cycfi/xr/XR_Controls/Blend_Control/Blend_Control_BOM.pdf

BLEND CONTROL
Item | Description | Part Number | Packaging | Manufacturer | Location | Qty.
1 | 25K Potentiometer | PDB181-GTR01-253A2 (http://www.mouser.ph/ProductDetail/Bourns/PDB181-GTR01-253A2/) | - | Bourns | POT1 | 1
2 | 1x3 SMD Male Header | M20-8900305 (http://www.mouser.ph/ProductDetail/Harwin/M20-8900305/) | 2.54mm | Harwin | H1 | 1
