cycfi/xr/XR_Controls/Volume_Control/Volume_Control_BOM.pdf

VOLUME CONTROL
Item | Description | Part Number | Packaging | Manufacturer | Location | Qty.
1 | 25K Potentiometer | PDB241-GTR01-253A2 (http://www.mouser.com/ProductDetail/Bourns/PDB241-GTR01-253A2/) | - | Bourns | POT1 | 1
2 | 1x5 SMD Male Header | M20-8900505 (http://www.mouser.com/ProductDetail/Harwin/M20-8900505/) | 2.54mm | Harwin | H1 | 1
