cycfi/xr/XR_Controls/Tone_Control/Tone_Control_BOM.pdf

TONE CONTROL
Item | Description | Part Number | Packaging | Manufacturer | Location | Qty.
1 | 25K Potentiometer | PDB181-GTR01-253A2 (http://www.mouser.ph/ProductDetail/Bourns/PDB181-GTR01-253A2/) | - | Bourns | POT1 | 1
2 | 1x2 Male Header RA | M20-9960245 (http://www.mouser.ph/ProductDetail/Harwin/M20-9960245/) | 2.54mm | Harwin | H1 | 1
3 | 0.1uF | VJ0603Y104JXJPW1BC (http://www.mouser.ph/ProductDetail/Vishay-Vitramon/VJ0603Y104JXJPW1BC/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) | SMD 0603 | Vishay | C1 | 1
