cycfi/xr/5_Way_Flex_Switch/Configuration_board/Configuration_board_A/Configuration_Board_A_Schematics.pdf

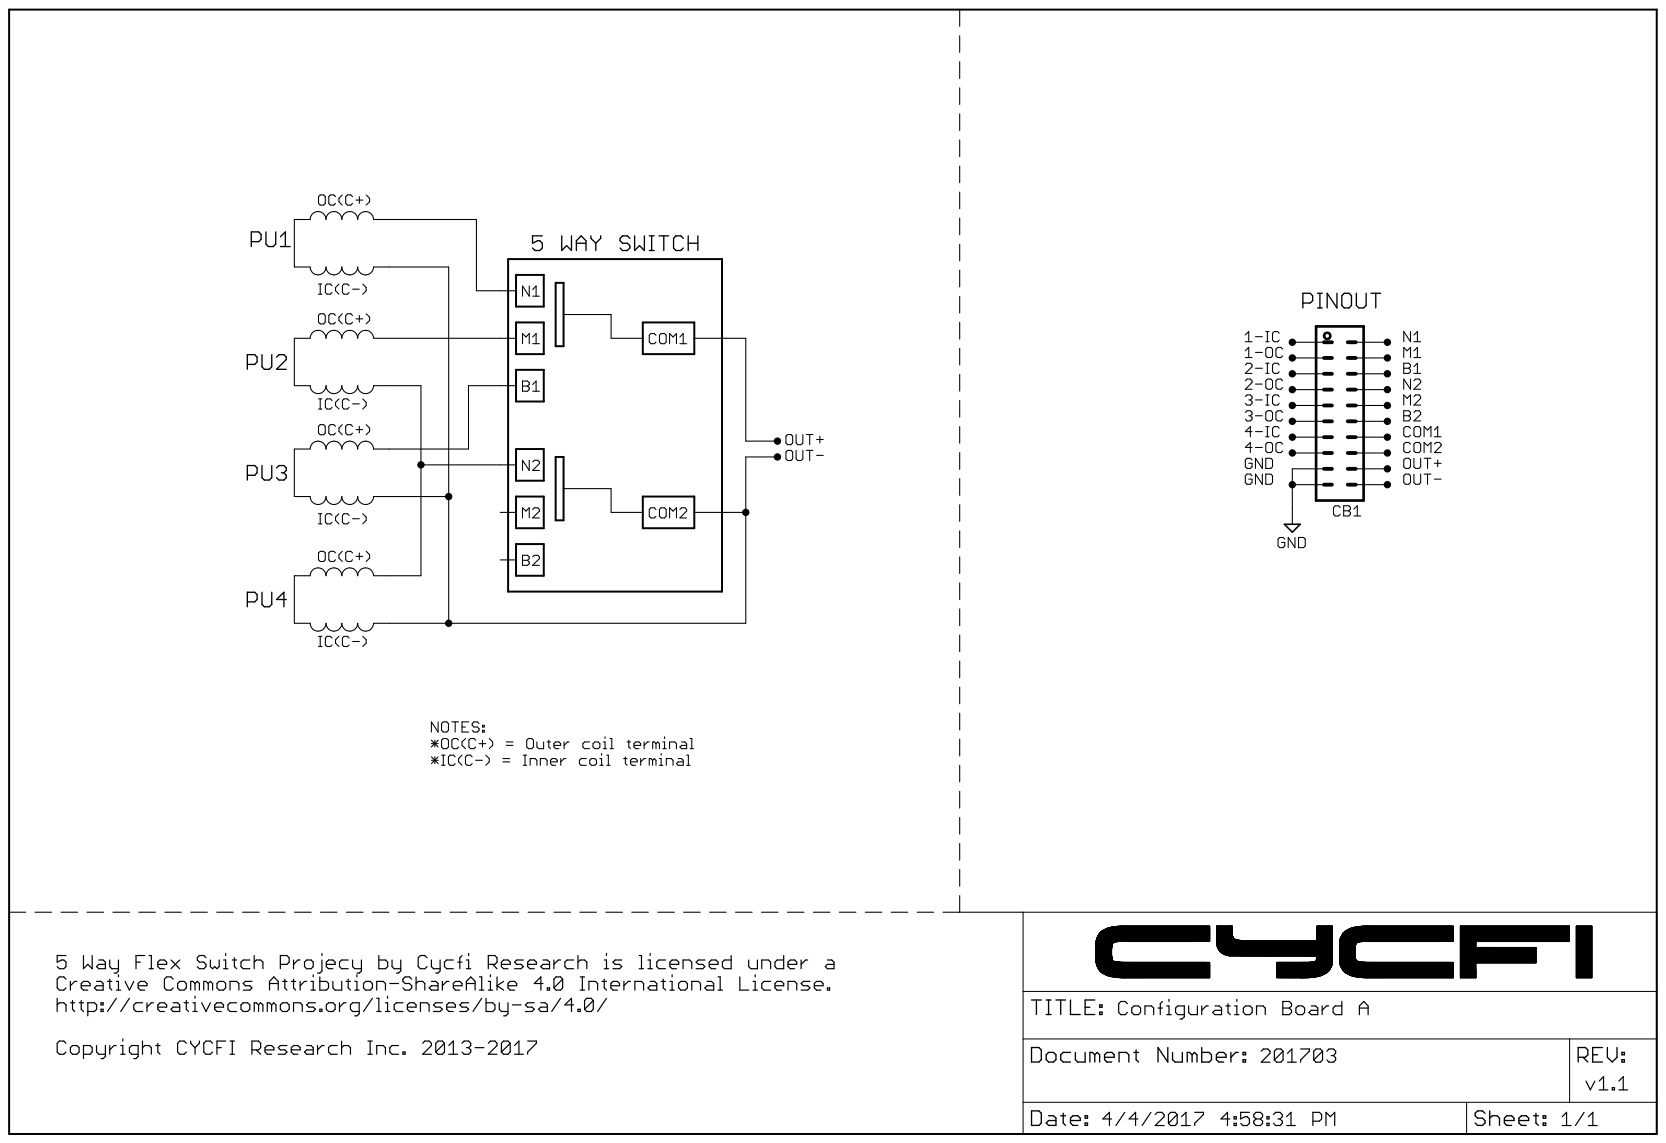
[picture p23: page 1]
