cycfi/xr/5_Way_Flex_Switch/Configuration_board/Configuration_board_B/Configuration_Board_B_Schematics.pdf

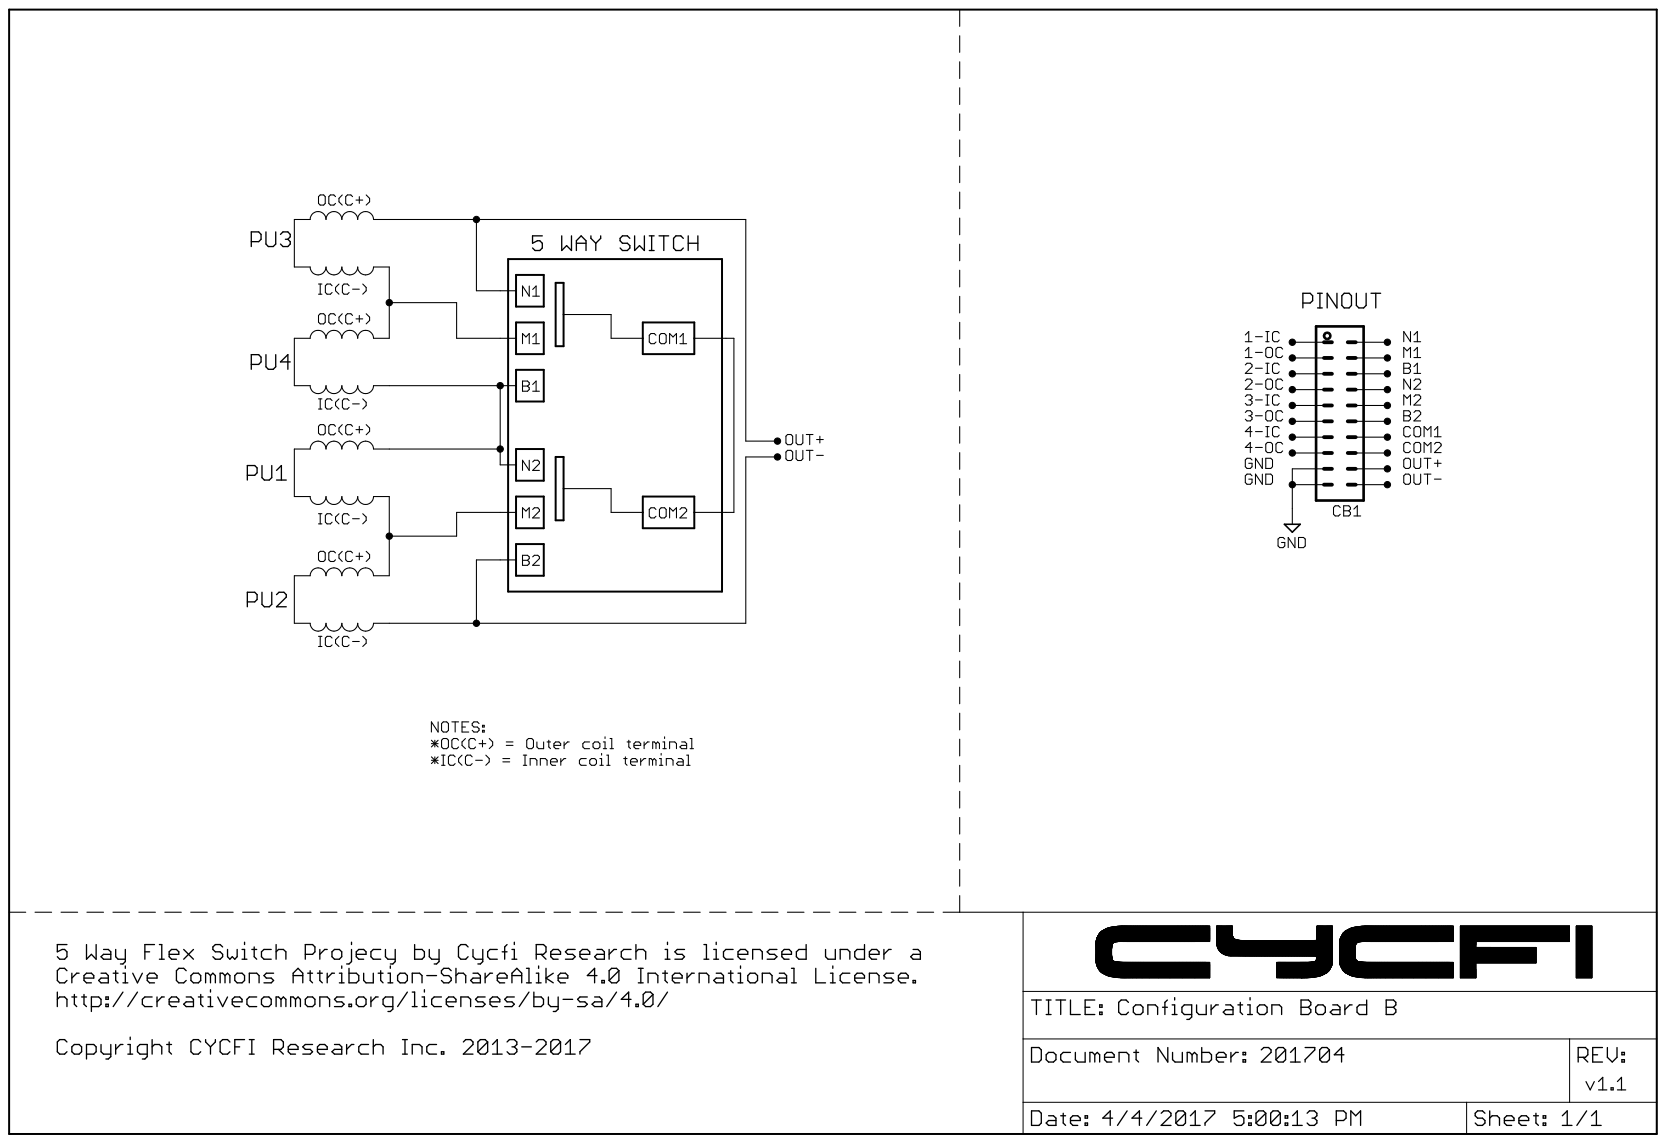
[picture p24: page 1]
