cycfi/xr/CAD_Drawings/Baseplate/Dual.pdf

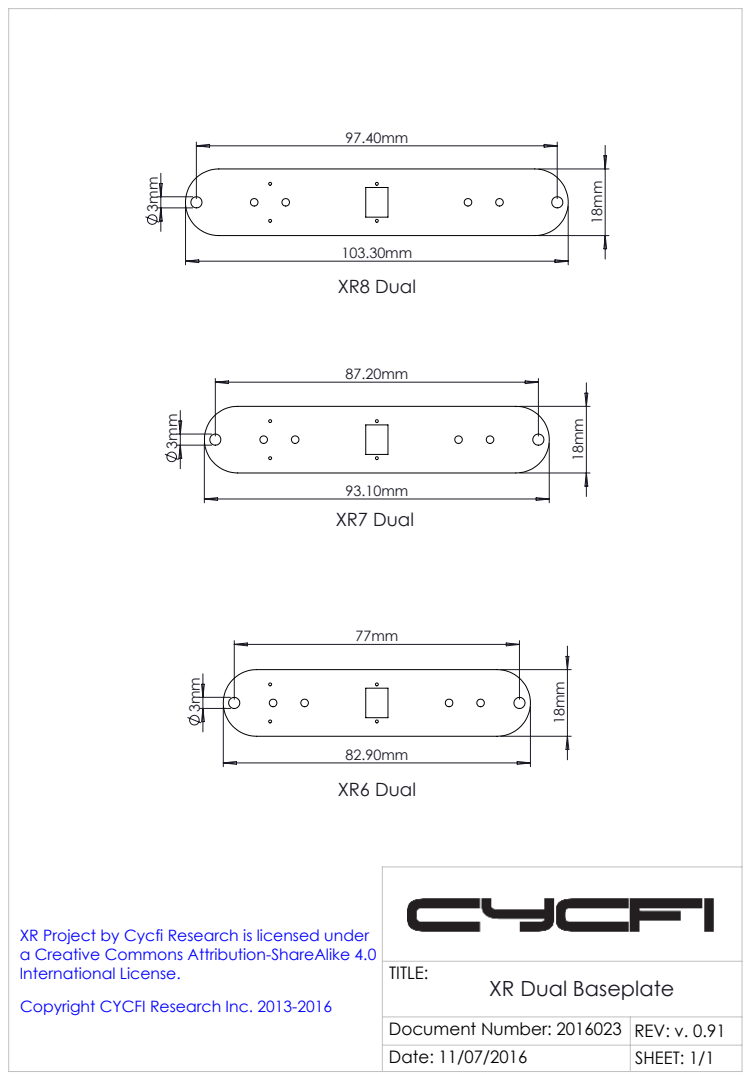
[picture p25: page 1]
XR6 Dual; XR7 Dual; XR8 Dual

XR Project by Cycfi Research is licensed under
a Creative Commons Attribution-ShareAlike 4.0
International License.
Copyright CYCFI Research Inc. 2013-2016 (http://creativecommons.org/licenses/by-sa/4.0/)

XR Dual Baseplate

Document Number: 2016023 | REV: v. 0.91
Date: 11/07/2016 | SHEET: 1/1
