cycfi/xr/CAD_Drawings/Baseplate/Half_Soapbar.PDF

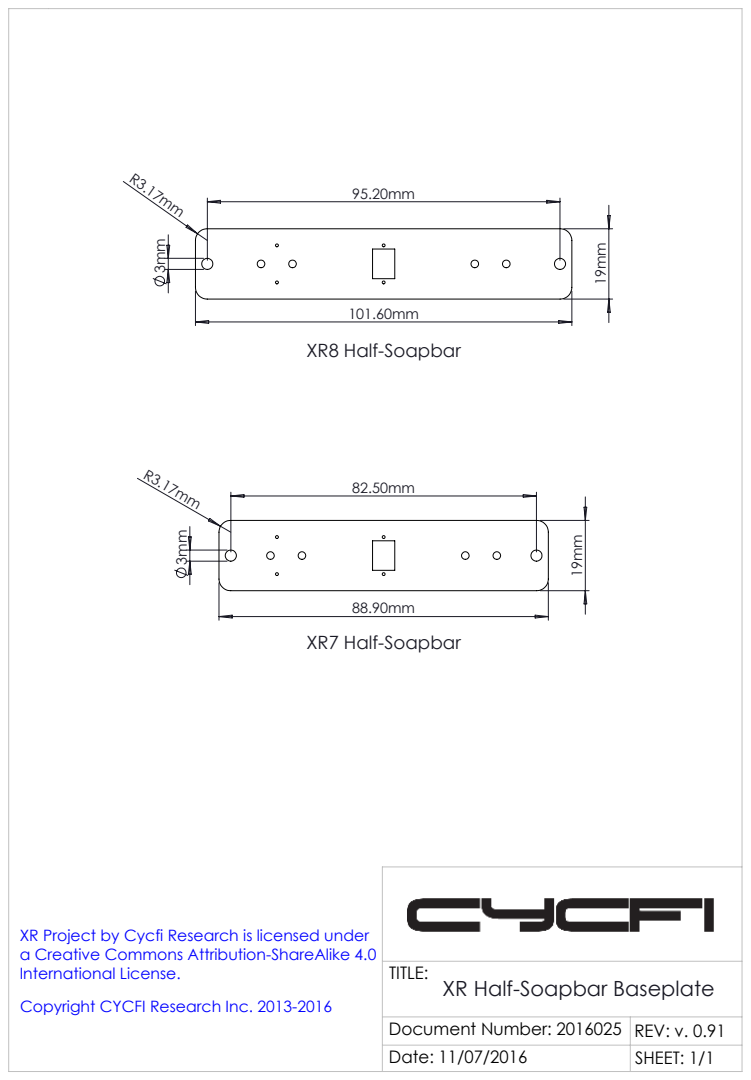
[picture p26: page 1]
XR7 Half-Soapbar; XR8 Half-Soapbar

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

TITLE:
XR Half-Soapbar Baseplate

Document Number: 2016025 | REV: v. 0.91
Date: 11/07/2016 | SHEET: 1/1
