cycfi/xr/CAD_Drawings/Baseplate/Quad.pdf

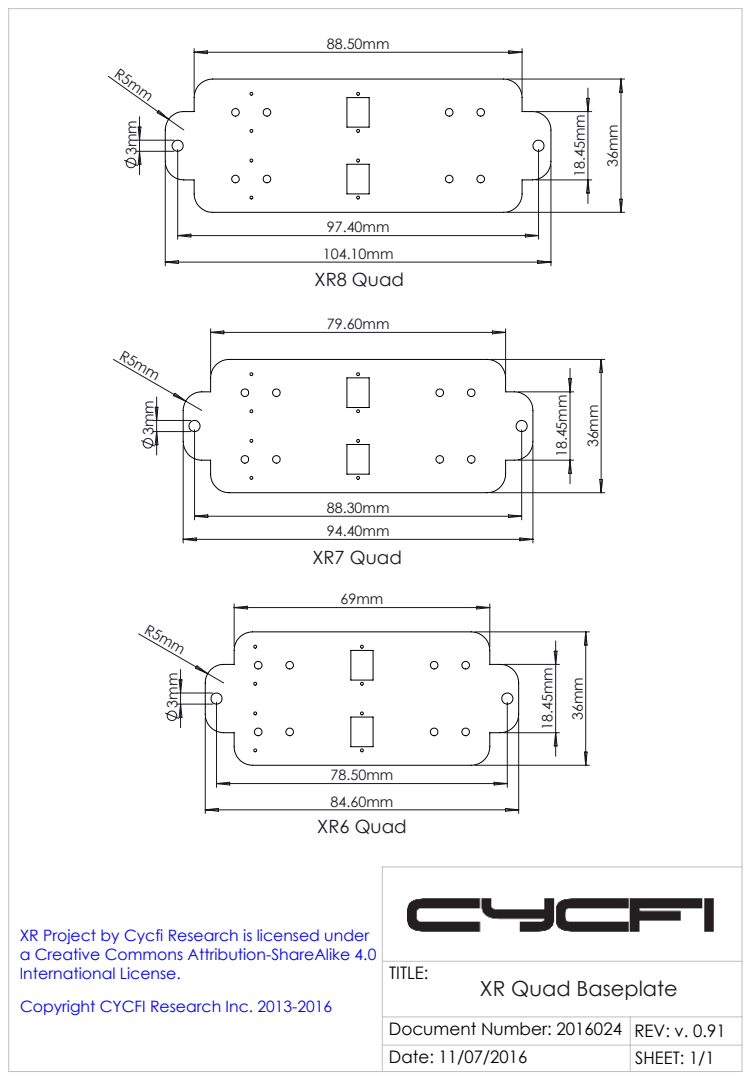
[picture p27: page 1]
XR6 Quad; XR7 Quad; XR8 Quad

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

XR Quad Baseplate

Document Number: 2016024 | REV: v. 0.91
Date: 11/07/2016 | SHEET: 1/1
