cycfi/xr/CAD_Drawings/Baseplate/Soapbar.pdf

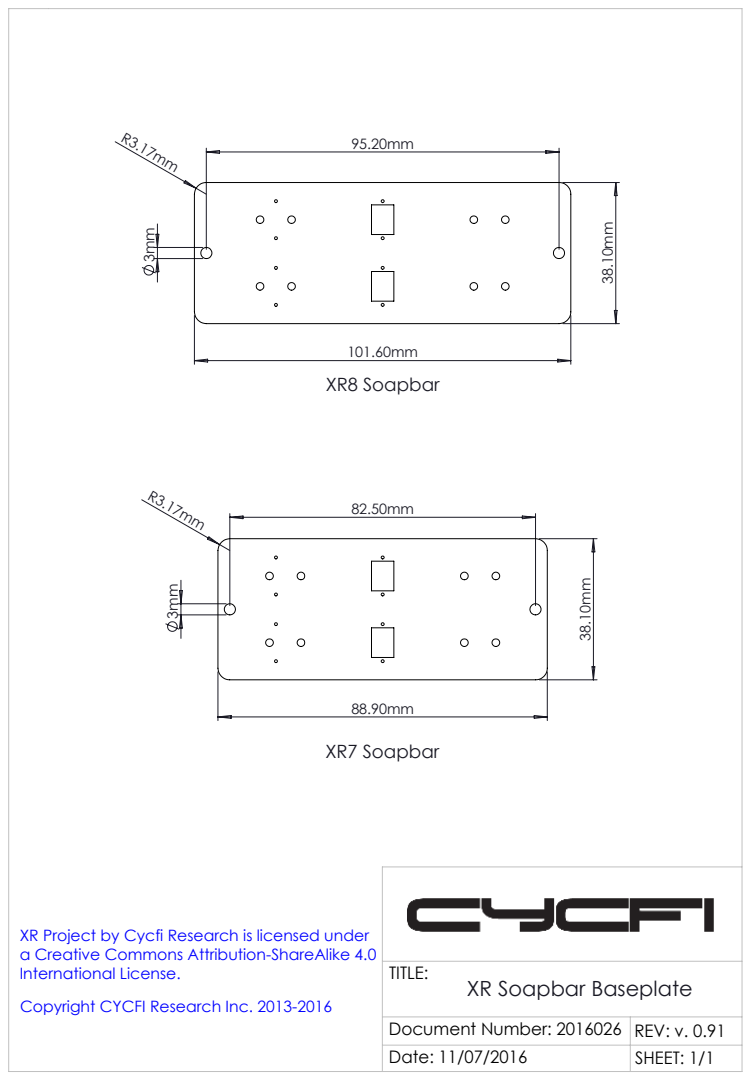
[picture p28: page 1]
XR7 Soapbar; XR8 Soapbar

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

TITLE:
XR Soapbar Baseplate

Document Number: 2016026 | REV: v. 0.91
Date: 11/07/2016 | SHEET: 1/1
