cycfi/xr/CAD_Drawings/XR_Dual/XR6_Dual_Drawing.pdf

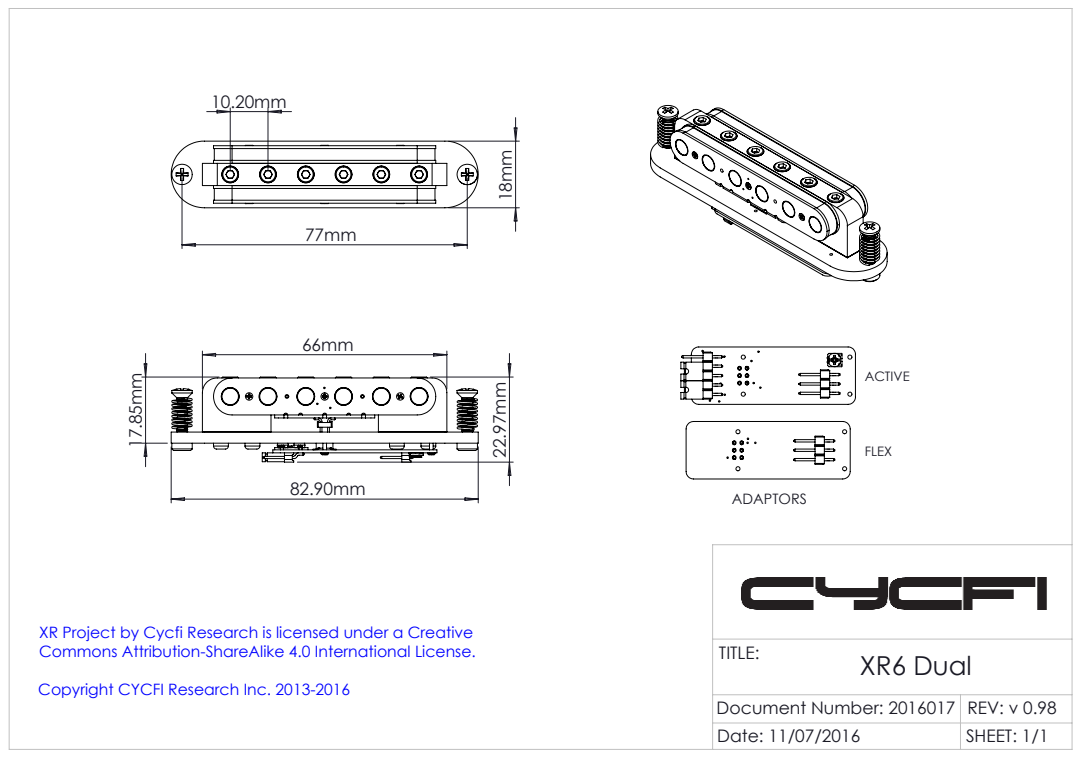
[picture p29: page 1]
XR6 Dual TITLE:

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

Document Number: 2016017 | REV: v 0.98
Date: 11/07/2016 | SHEET: 1/1
