cycfi/xr/CAD_Drawings/XR_Dual/XR7_Dual_Drawing.pdf

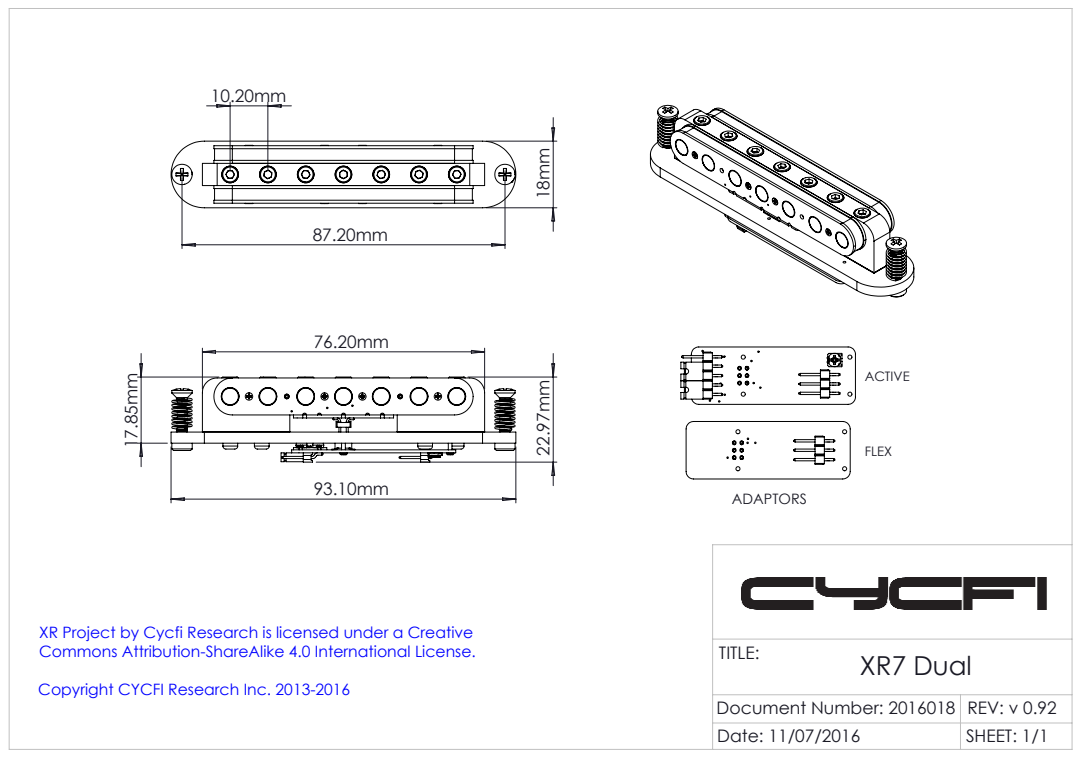
[picture p30: page 1]
XR7 Dual TITLE:

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

Document Number: 2016018 | REV: v 0.92
Date: 11/07/2016 | SHEET: 1/1
