cycfi/xr/CAD_Drawings/XR_Half_Soapbar/XR7_Half_Soapbar_Drawing.pdf

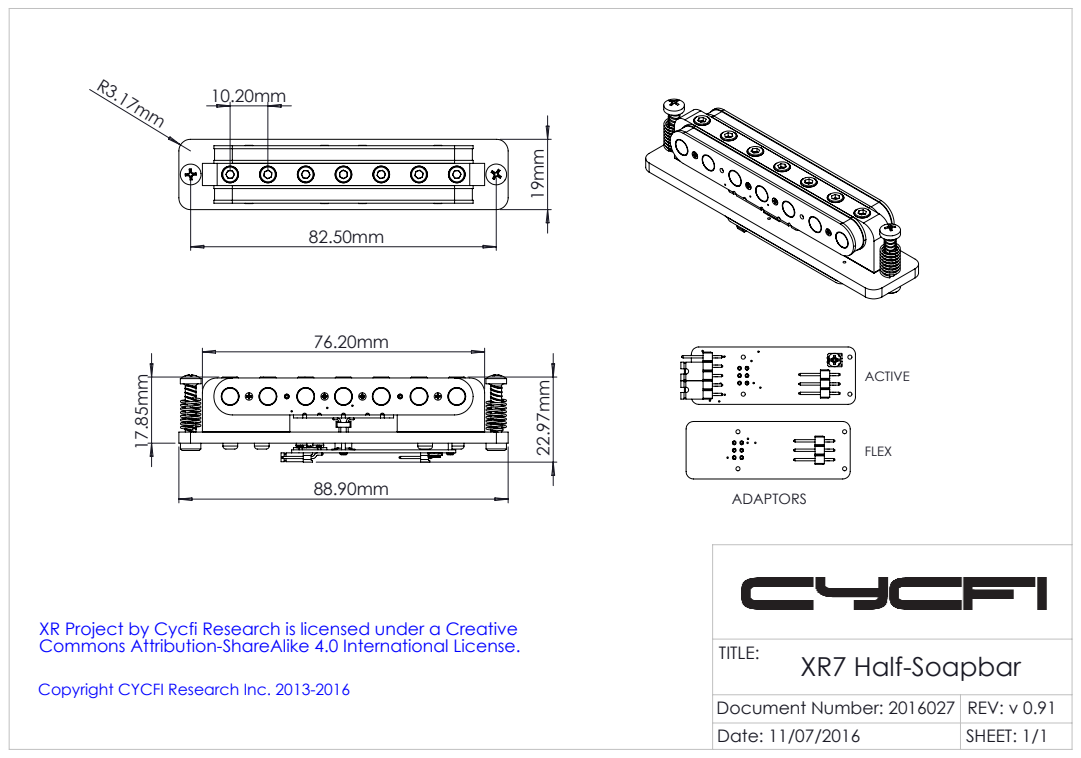
[picture p31: page 1]
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

XR7 Half-Soapbar TITLE:

Copyright CYCFI Research Inc. 2013-2016 (http://creativecommons.org/licenses/by-sa/4.0/)

Document Number: 2016027 | REV: v 0.91
Date: 11/07/2016 | SHEET: 1/1
