cycfi/xr/CAD_Drawings/XR_Half_Soapbar/XR8_Half_Soapbar_Drawing.pdf

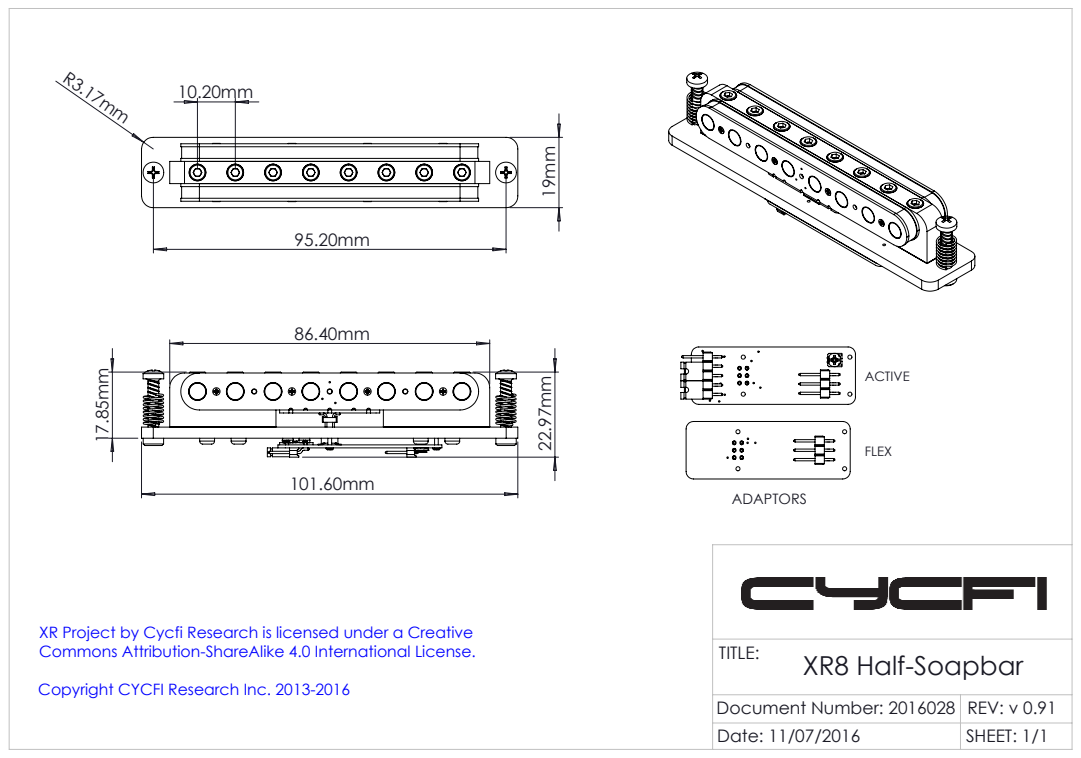
[picture p32: page 1]
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

XR8 Half-Soapbar TITLE:

Document Number: 2016028 | REV: v 0.91
Date: 11/07/2016 | SHEET: 1/1
