cycfi/xr/CAD_Drawings/XR_Quad/XR6_Quad_Drawing.pdf

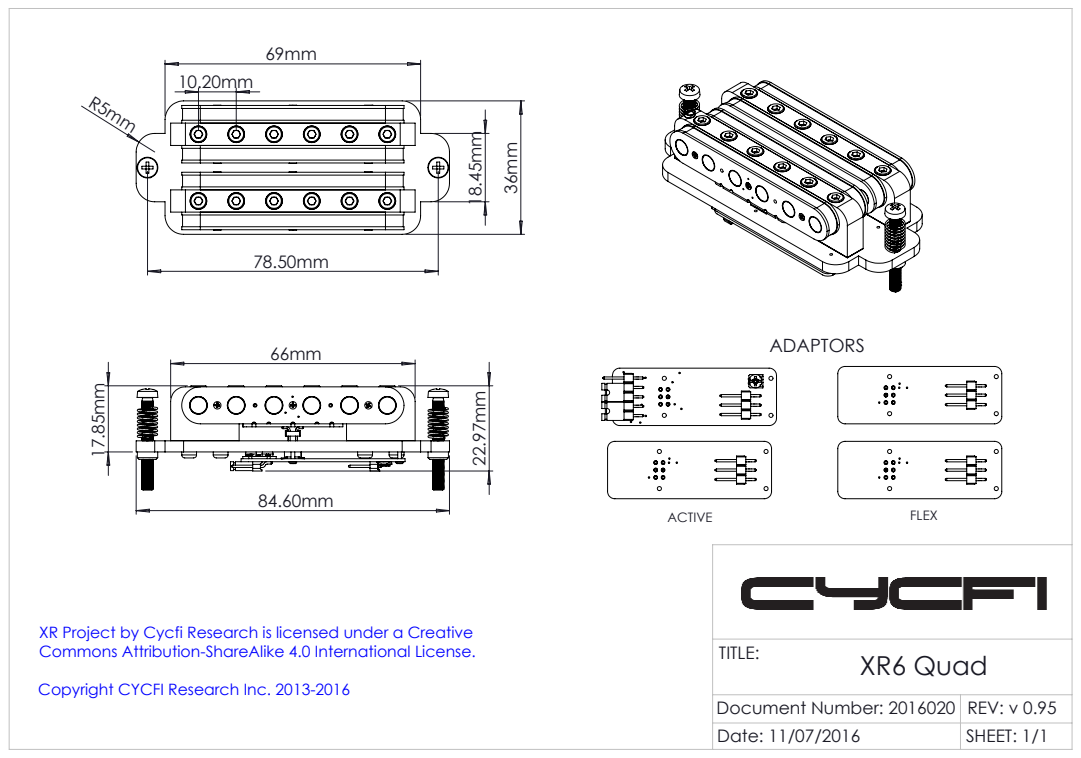
[picture p33: page 1]
XR6 Quad TITLE:

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

Document Number: 2016020 | REV: v 0.95
Date: 11/07/2016 | SHEET: 1/1
