cycfi/xr/Toggle_Switch_Hub/Toggle_Switch_Hub.brd

## EAGLE design Toggle_Switch_Hub/Toggle_Switch_Hub.brd (2016-02-18)

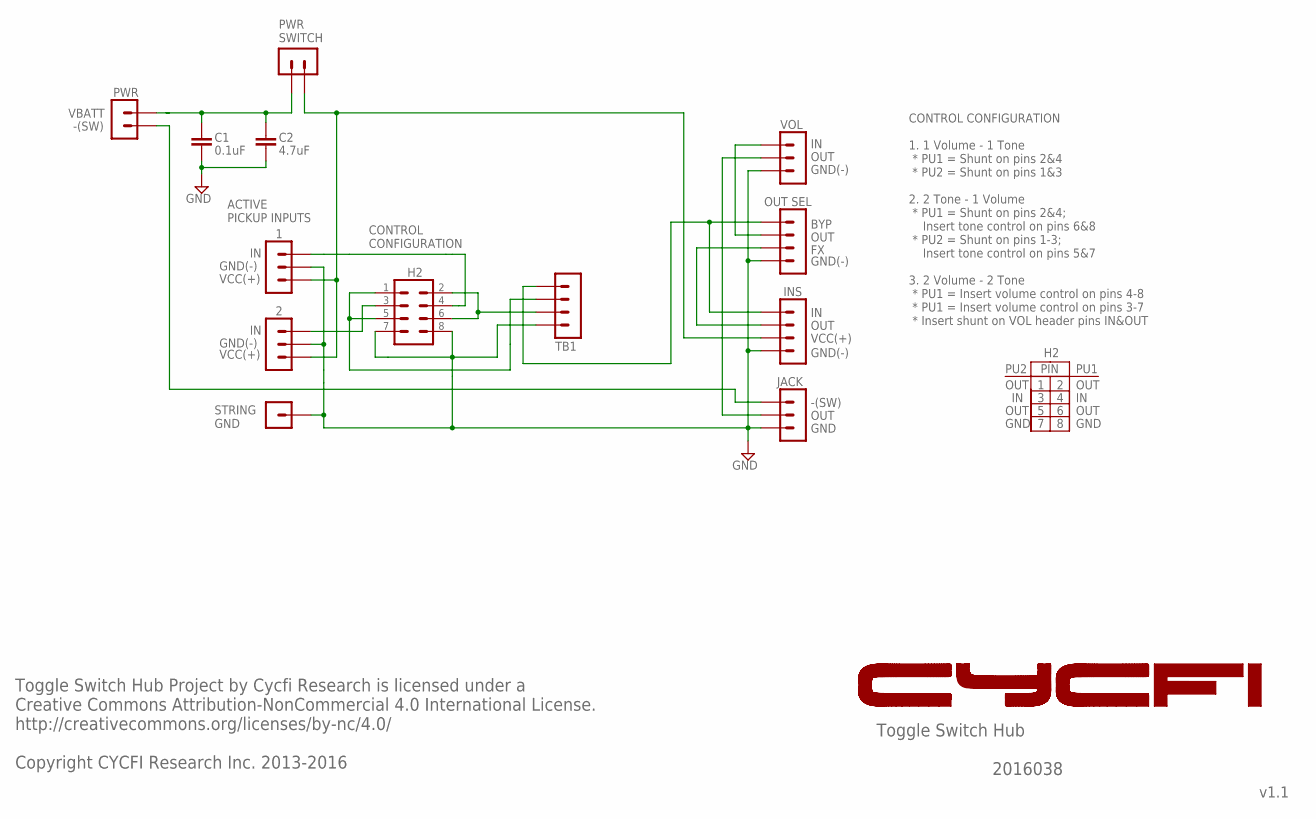
[picture p59: schematic Toggle_Switch_Hub.sch, sheet 1]

Parts:
C1: 0.1uF; C0603
C2: 4.7uF; C0603
H2: MA04-2
TB1: 282837-4_TERMINAL_BLOCK; TERMINAL_BLOCK_4P_5.08MM

Connections:
BYP: TB1.P$4 (4); also elsewhere on the board
GND: C1.2, C2.2, H2.7, H2.8, TB1.P$1 (1); also elsewhere on the board
unnamed: H2.2, H2.6, TB1.P$2 (2)
unnamed: H2.1, H2.5, TB1.P$3 (3)
PU1: H2.4; also elsewhere on the board
PU2: H2.3; also elsewhere on the board
VCC: C1.1, C2.1; also elsewhere on the board

Notes on the sheet:
GND(-)
VCC(+)
CONTROL CONFIGURATION
BYP
OUT
-(SW)
GND
VOL
INS
JACK
OUT SEL
PWR SWITCH
ACTIVE PICKUP INPUTS
VBATT
TB1
PWR
PU1
PIN
CONTROL CONFIGURATION 1. 1 Volume - 1 Tone * PU1 = Shunt on pins 2&4 * PU2 = Shunt on pins 1&3 2. 2 Tone - 1 Volume * PU1 = Shunt on pins 2&4; Insert tone control on pins 6&8 * PU2 = Shunt on pins 1-3; Insert tone control on pins 5&7 3. 2 Volume - 2 Tone * PU1 = Insert volume control on pins 4-8 * 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
PU2
STRING GND
Toggle Switch Hub
v1.1
Toggle Switch Hub Project by Cycfi Research is licensed under a Creative Commons Attribution-NonCommercial 4.0 International License. http://creativecommons.org/licenses/by-nc/4.0/ Copyright CYCFI Research Inc. 2013-2016
2016038

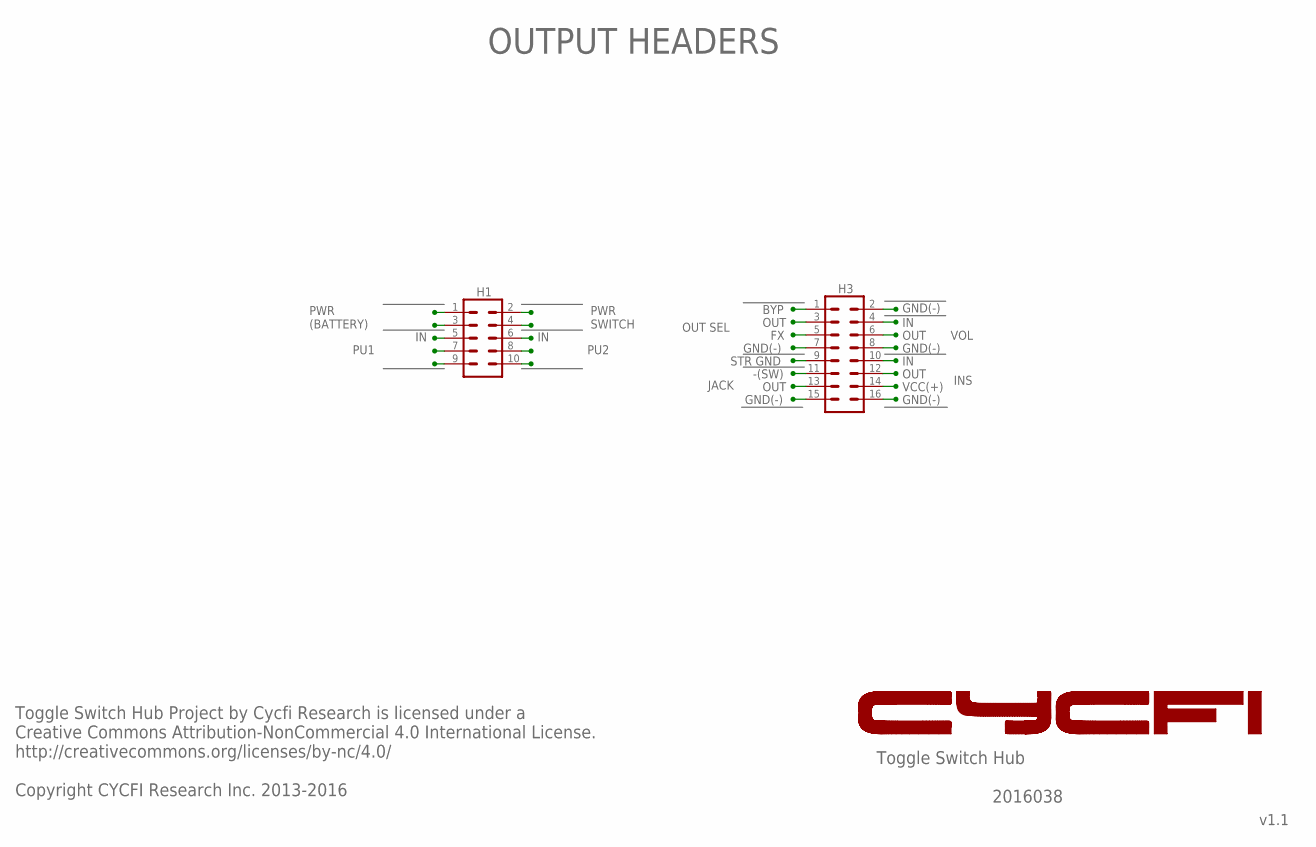
[picture p60: schematic Toggle_Switch_Hub.sch, sheet 2]

Parts:
H1: MA05-2
H3: MA08-2

Connections:
BYP: H3.1, H3.10; also elsewhere on the board
FX: H3.5, H3.12
GND: H1.7, H1.8, H3.2, H3.7, H3.8, H3.9, H3.15, H3.16; also elsewhere on the board
OUT: H3.3, H3.4
OUT(VOL): H3.6, H3.13
PU1: H1.5; also elsewhere on the board
PU2: H1.6; also elsewhere on the board
SW: H1.3, H3.11
VCC: H1.1, H1.2; also elsewhere on the board
VIN: H1.4, H1.9, H1.10, H3.14

Notes on the sheet:
GND(-)
OUT
VCC(+)
-(SW)
BYP
STR GND
OUTPUT HEADERS
PWR (BATTERY)
PU1
PU2
PWR SWITCH
OUT SEL
JACK
VOL
INS
Toggle Switch Hub
v1.1
Toggle Switch Hub Project by Cycfi Research is licensed under a Creative Commons Attribution-NonCommercial 4.0 International License. http://creativecommons.org/licenses/by-nc/4.0/ Copyright CYCFI Research Inc. 2013-2016
2016038

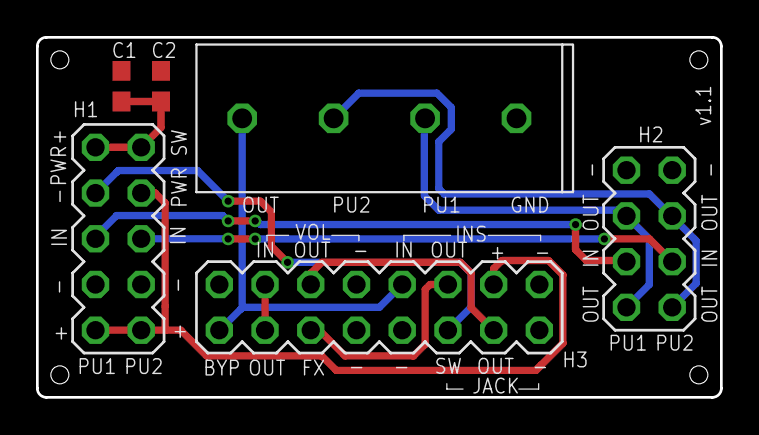
[picture p61: board Toggle_Switch_Hub.brd from above]

Board: 2 copper layers, 38.0 x 20.0 mm, 6 parts (0 on the bottom side), 12 nets.
